hacklabkyiv/prismo-reader/3dmodels/logout_button.stl

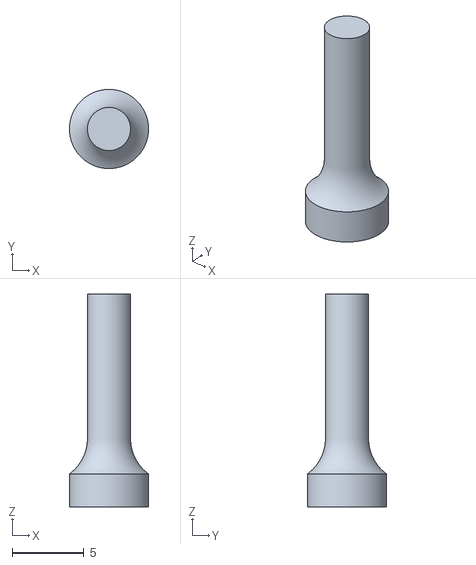
[picture p18: CAD file, 2025-07-29]
3dmodels/logout_button.stl
5.50 x 5.50 x 14.8
