hacklabkyiv/prismo-reader/3dmodels/outside_sensor_holder_print_screw_plug.stl

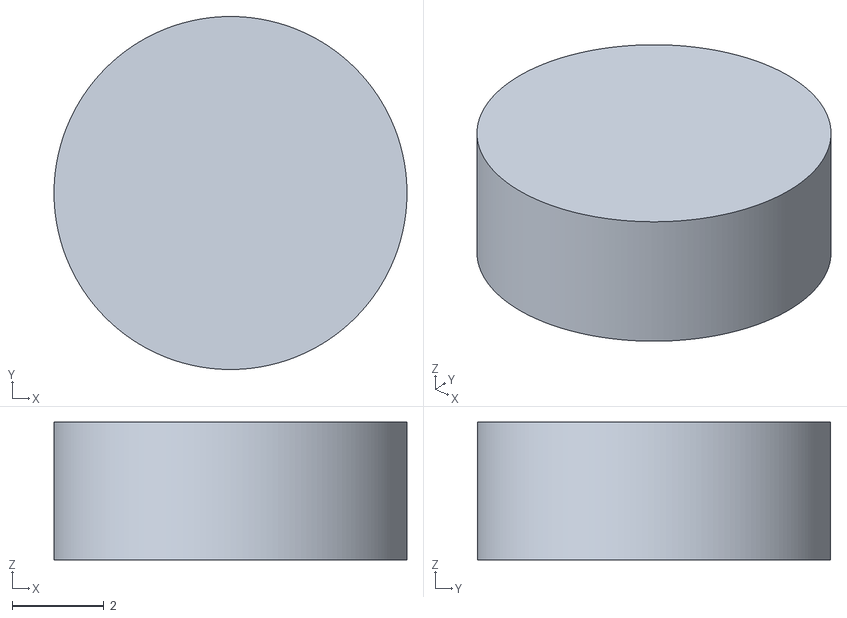
[picture p19: CAD file, 2025-07-29]
3dmodels/outside_sensor_holder_print_screw_plug.stl
7.70 x 7.70 x 3.00
