hacklabkyiv/prismo-reader/src/main.py

__author__ = "sashkoiv"
__copyright__ = "Copyright 2023, KyivHacklab"
__credits__ = ["artsin", "sashkoiv", "paulftw", "lazer_ninja", "Vova Stelmashchuk", "Sayorus"]


from lib.kernel import Kernel

Kernel.main()
