hacklabkyiv/prismo-reader/firmware/include/settings.h

/*
 * RFID settings
 */

#ifndef _SETTINGS_h_
#define _SETTINGS_h_

//#define HW_TEST


#define STASSID "HackLab"
#define STAPSK  "derparol"

#define HOSTNAME "TestReader"
#define HOST "192.168.1.115"

#define MACHINE_NAME "mill"
#define PORT 9999

#define HEARTBEAT_INTERVAL 100000 // milliseconds

#endif /* _SETTINGS_h_ */
